Helitha-Ruvinda/Analog-Audio-Spectrum-Analyzer/Media/BackView.jpeg

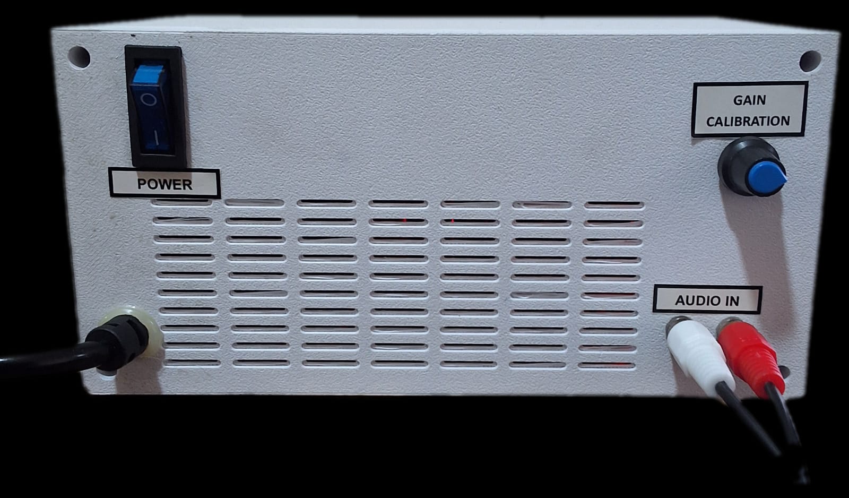
Media/BackView.jpeg
