Helitha-Ruvinda/Analog-Audio-Spectrum-Analyzer/Media/Breadboard implementation image 1.jpeg

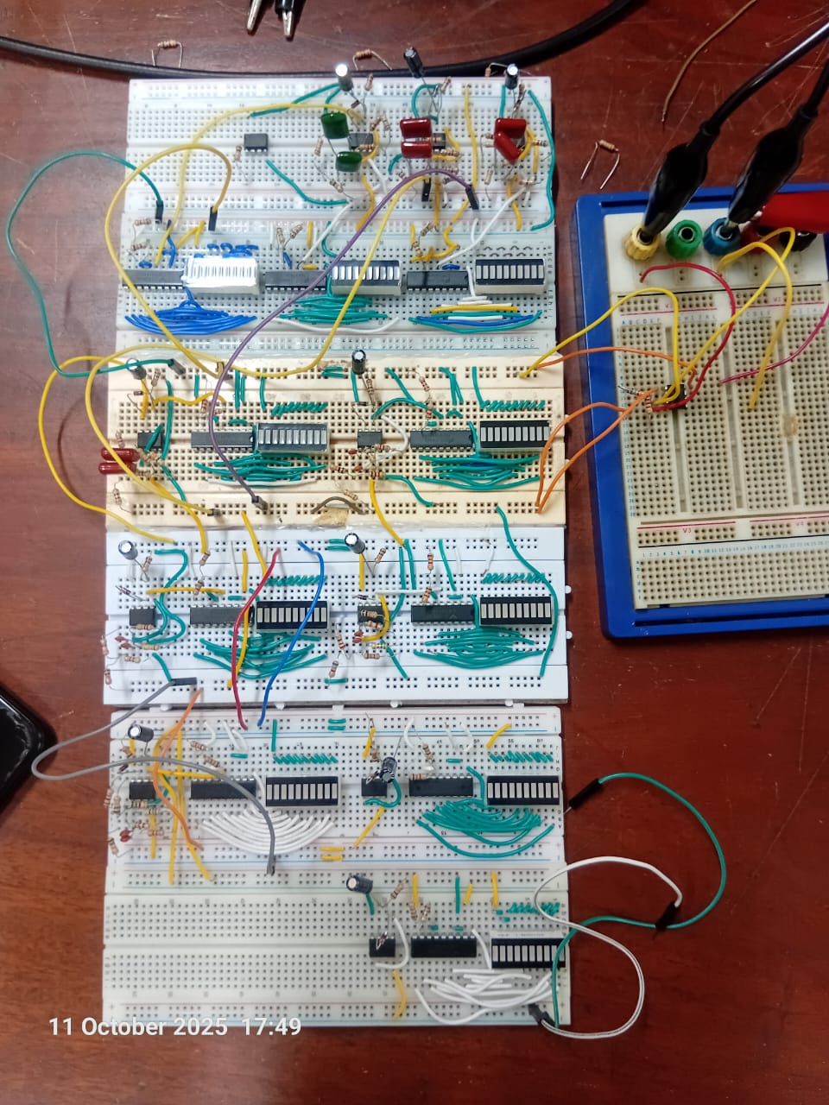
Media/Breadboard implementation image 1.jpeg
