Helitha-Ruvinda/Analog-Audio-Spectrum-Analyzer/Media/Breadboard implementation image 2.jpeg

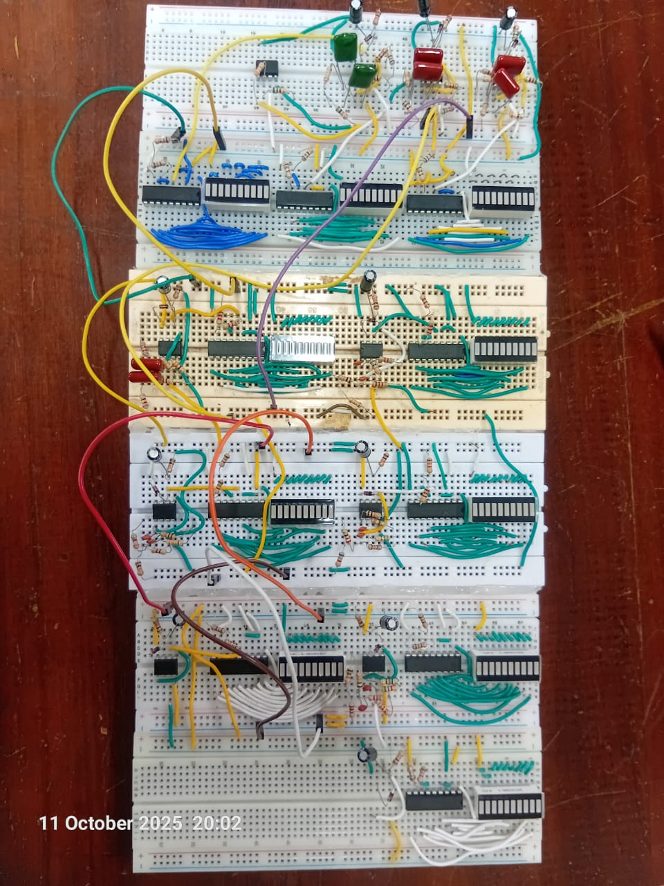
Media/Breadboard implementation image 2.jpeg
