Helitha-Ruvinda/Analog-Audio-Spectrum-Analyzer/Media/FrontView.jpeg

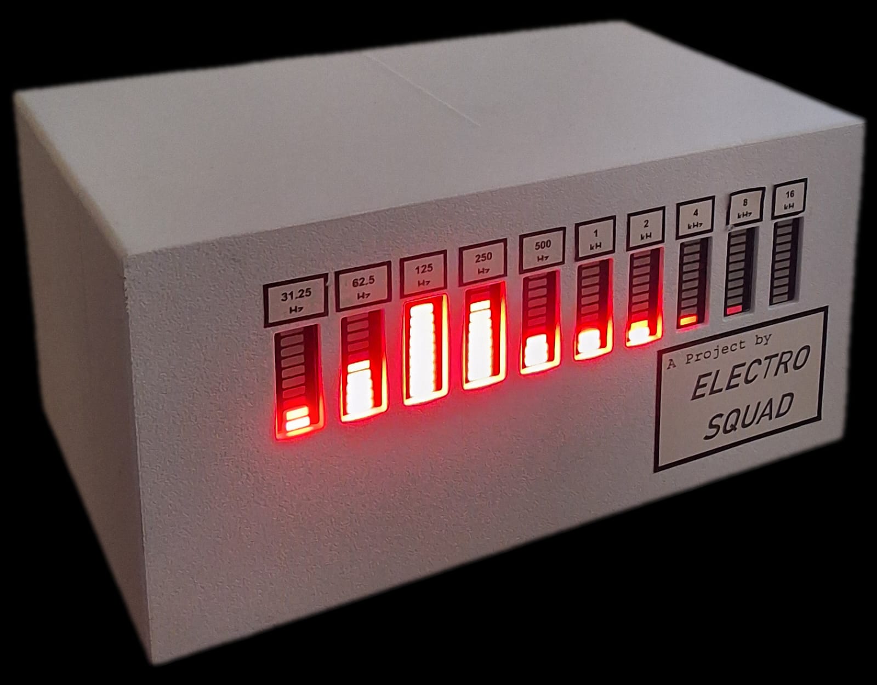
Media/FrontView.jpeg
