Helitha-Ruvinda/Analog-Audio-Spectrum-Analyzer/ProtoTypeTesting/InputVsOutput.jpeg

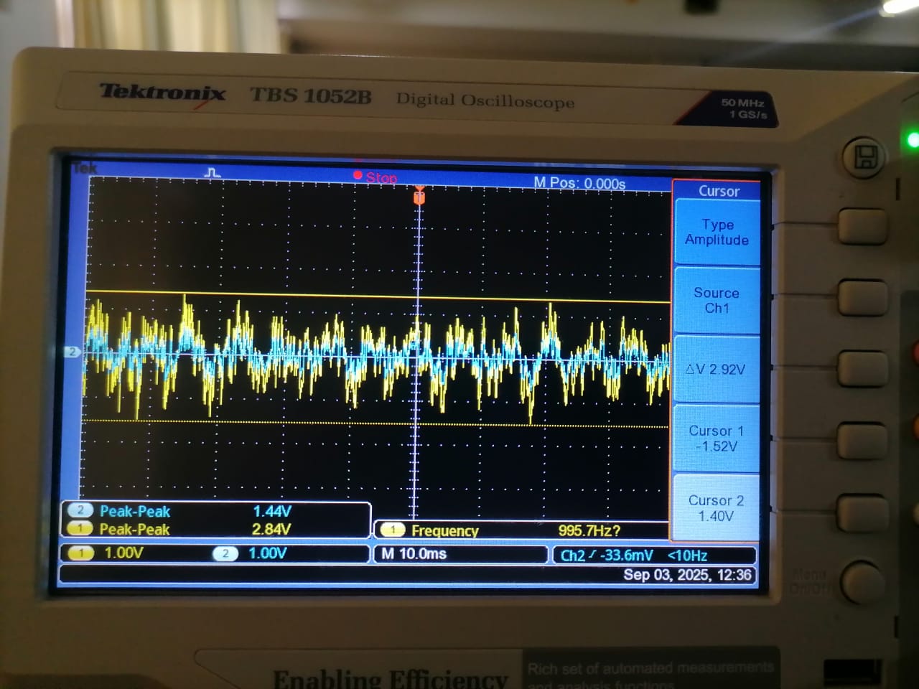
ProtoTypeTesting/InputVsOutput.jpeg
