Helitha-Ruvinda/Analog-Audio-Spectrum-Analyzer/ProtoTypeTesting/PeakDetectorOutput.jpeg

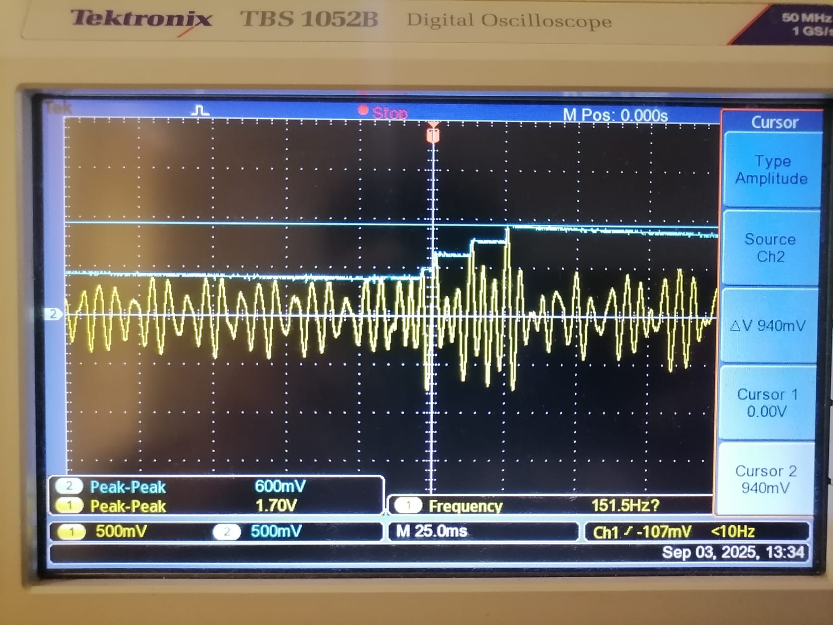
ProtoTypeTesting/PeakDetectorOutput.jpeg
